agnunez/HeliosCap/TestCap.stl

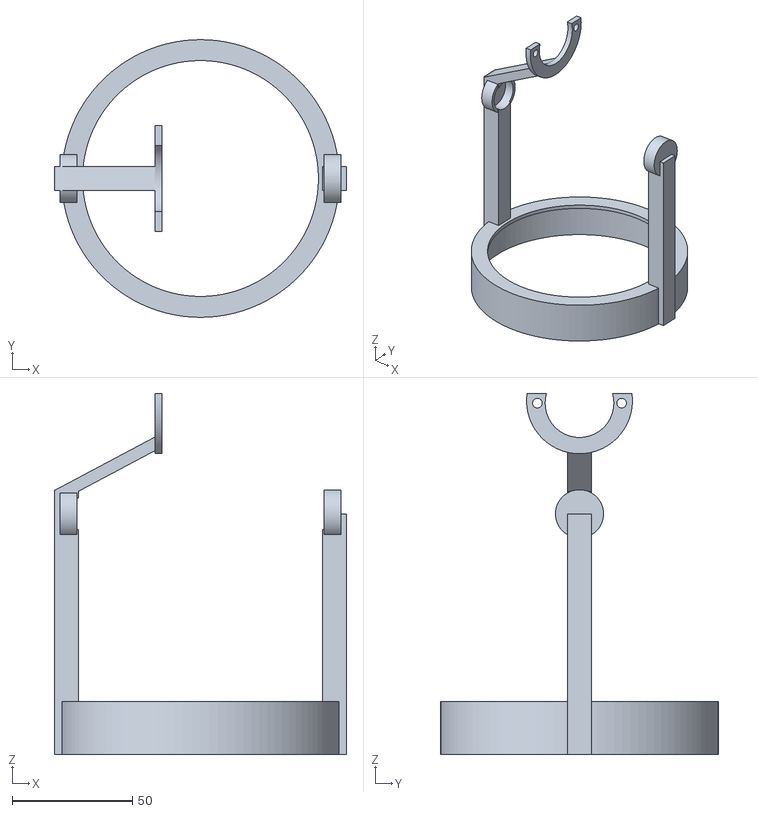
[picture p19: CAD file, 2020-05-06]
TestCap.stl
121.4 x 115.4 x 150.0
