agnunez/HeliosCap/MotorHolder.stl

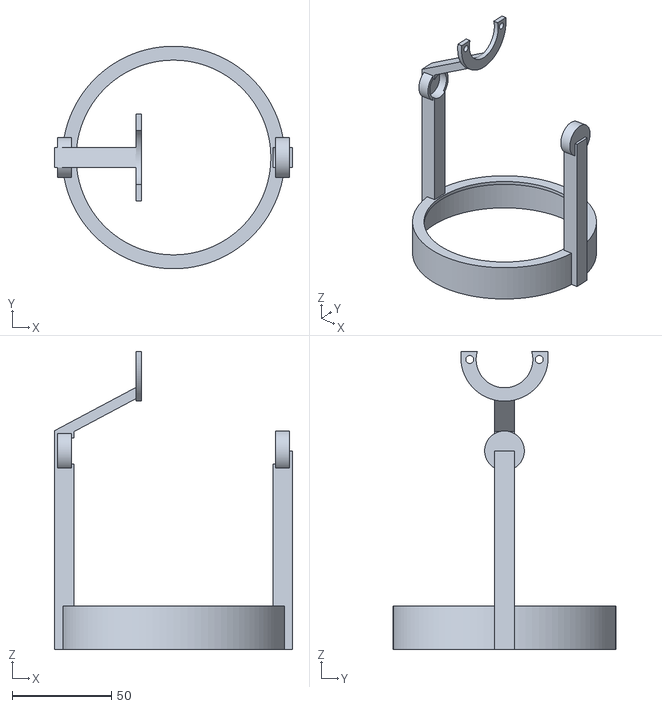
[picture p20: CAD file, 2020-05-05]
MotorHolder.stl
120.0 x 112.0 x 150.0
