agnunez/HeliosCap/MirrorGear.stl

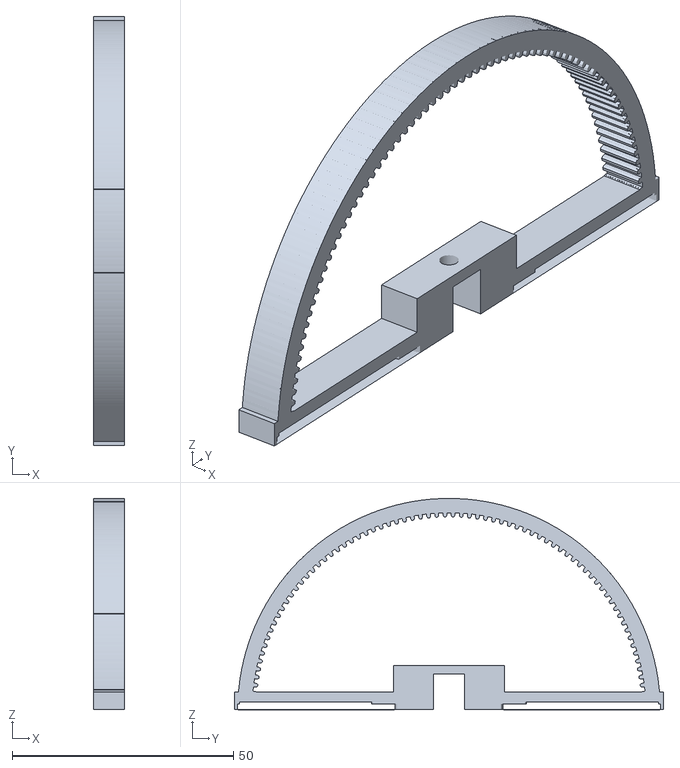
[picture p21: CAD file, 2020-05-05]
MirrorGear.stl
7.00 x 97.0 x 47.8
