agnunez/HeliosCap/MirrorHolder.stl

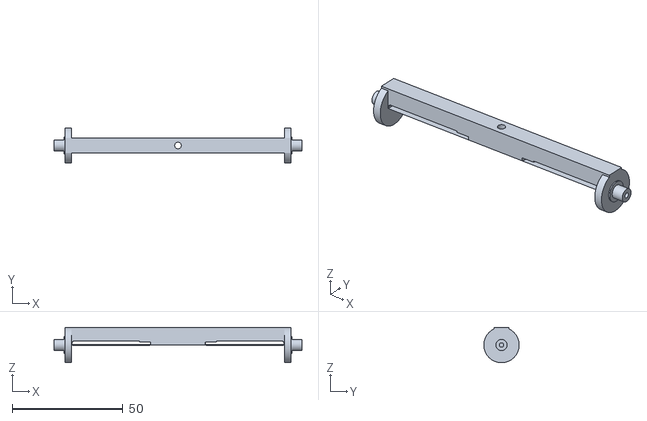
[picture p22: CAD file, 2020-05-04]
MirrorHolder.stl
112.0 x 16.0 x 16.0
