agnunez/HeliosCap/BearingCap.stl

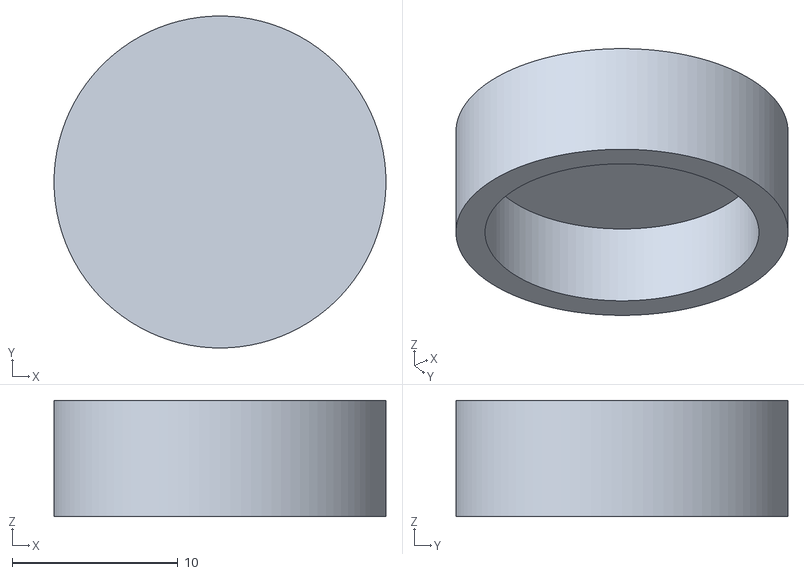
[picture p23: CAD file, 2020-05-04]
BearingCap.stl
20.0 x 20.0 x 7.00
