agnunez/HeliosCap/GT2-arc-test.stl

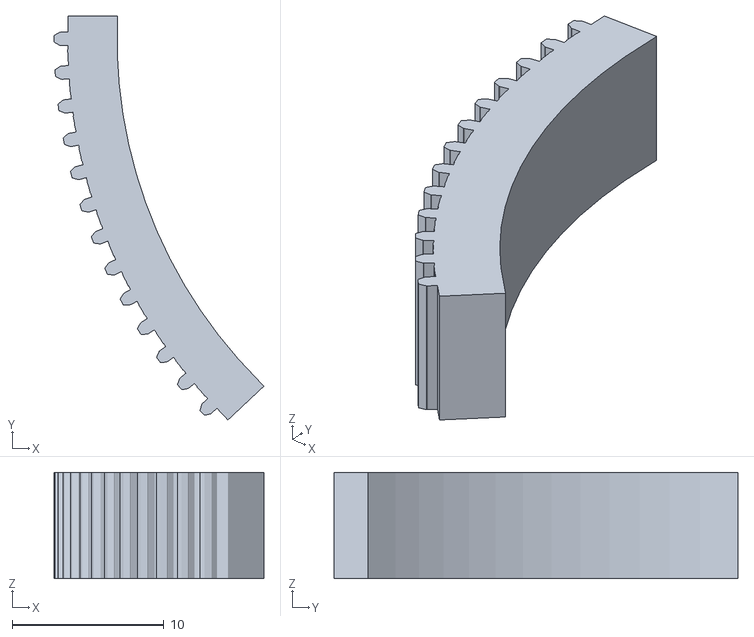
[picture p24: CAD file, 2020-05-03]
GT2-arc-test.stl
13.8 x 26.6 x 7.00
