agnunez/HeliosCap/MirrorShaft.stl

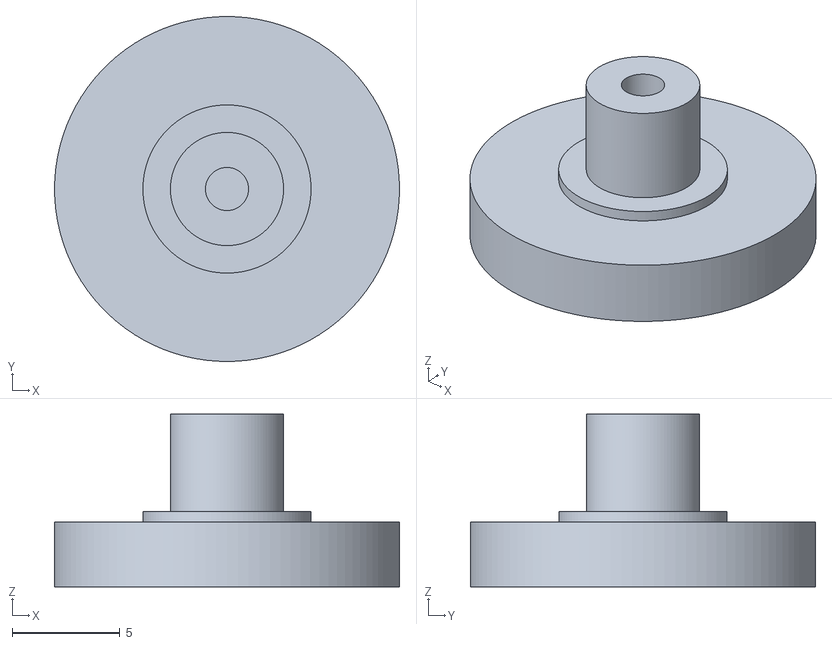
[picture p25: CAD file, 2020-05-02]
MirrorShaft.stl
16.0 x 16.0 x 8.00
