agnunez/HeliosCap/MirrorRetainer.stl

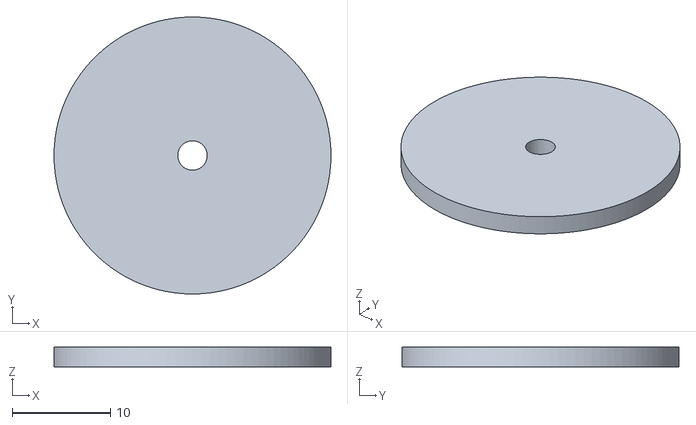
[picture p26: CAD file, 2020-05-02]
MirrorRetainer.stl
28.2 x 28.2 x 2.00
